twopoint718/pomodoro-timer/pomodorov2/pomodorov2.kicad_sch

## KiCad design pomodorov2/pomodorov2.kicad_sch (2022-04-18)

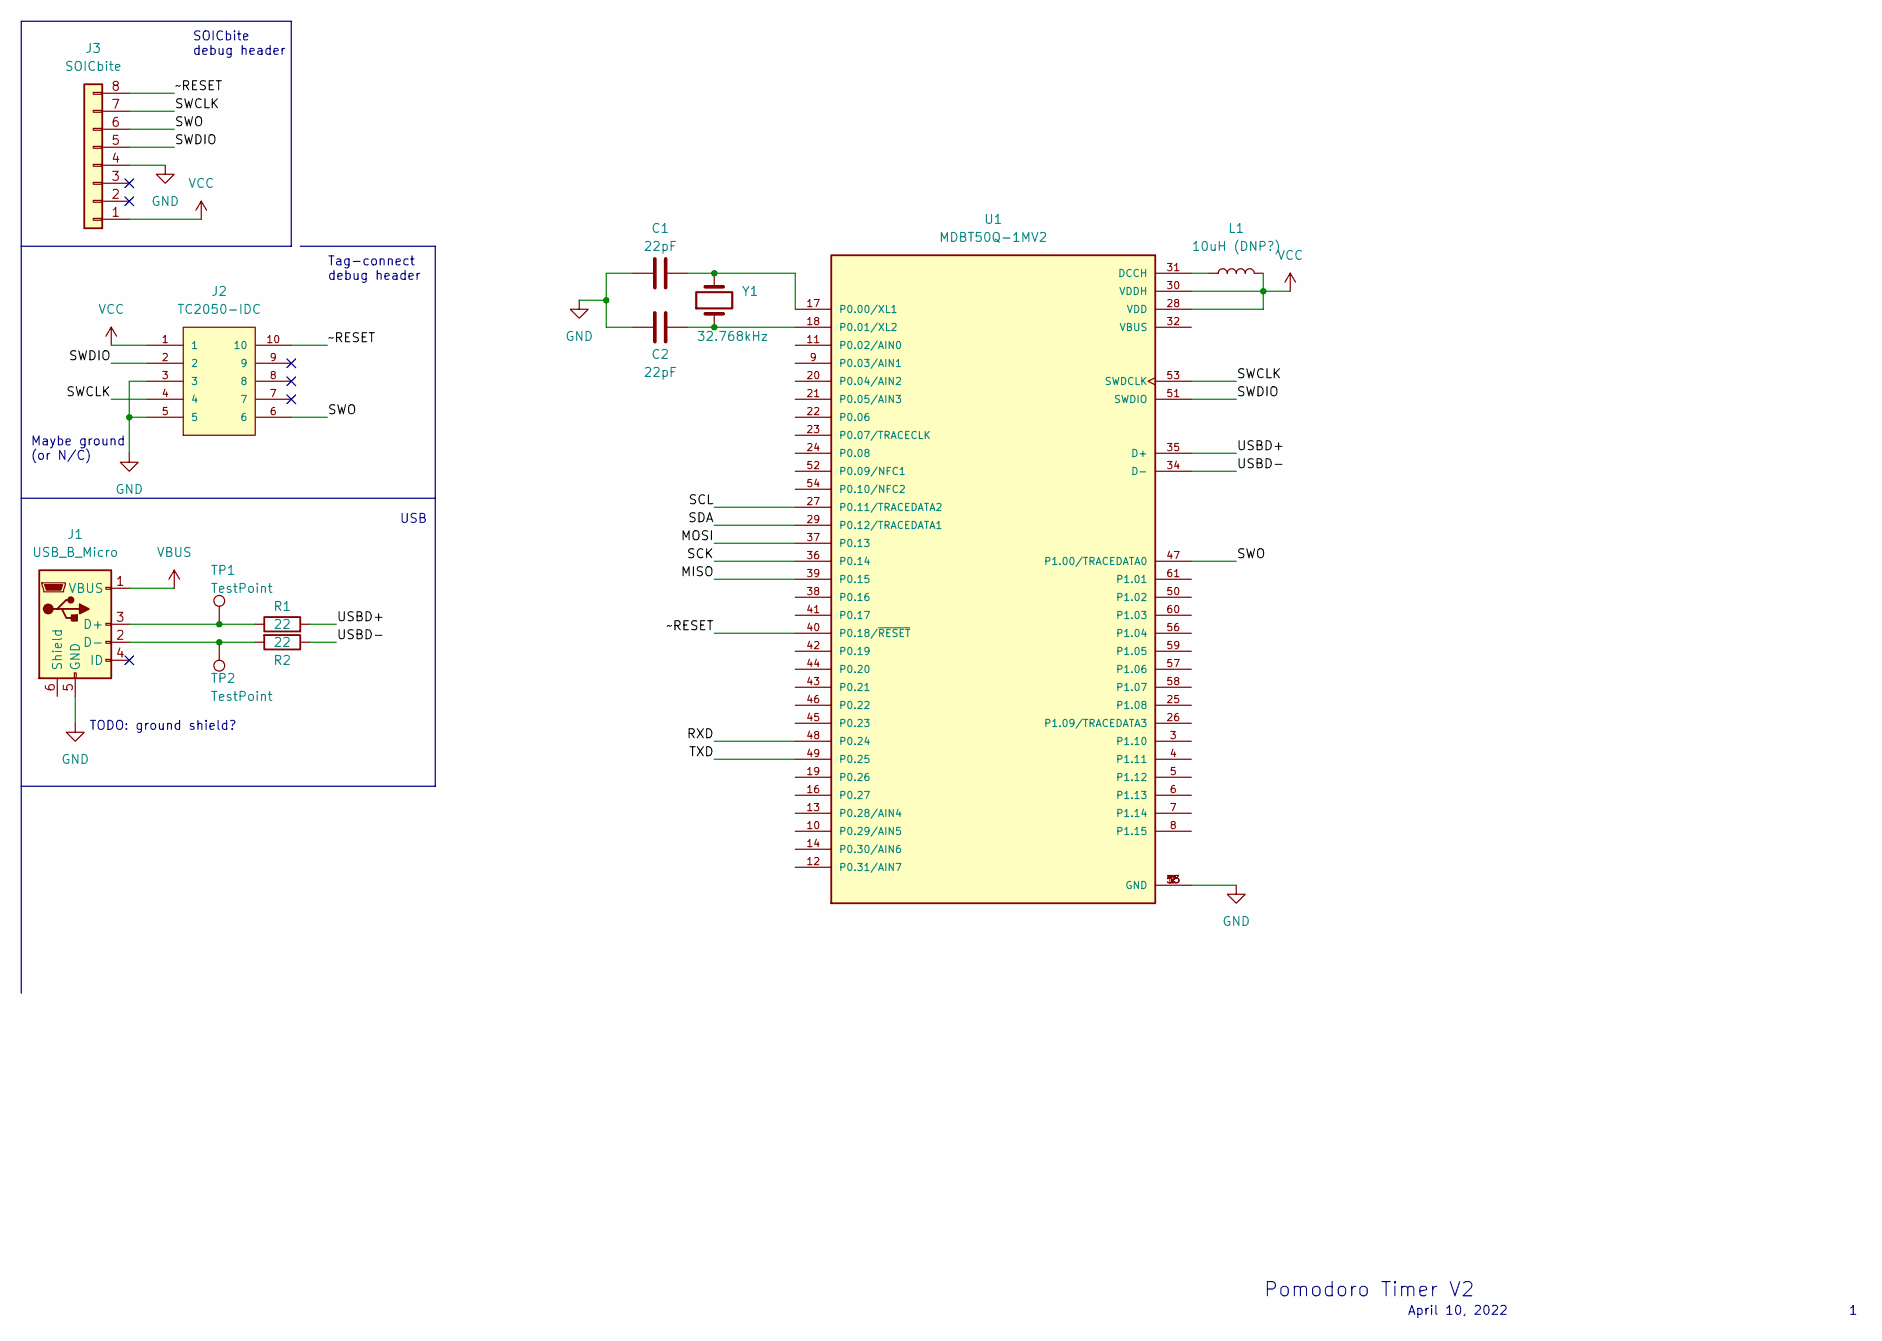
[picture p4: schematic pomodorov2.kicad_sch]

Parts:
C1, C2: 22pF; C_0805_2012Metric_Pad1.18x1.45mm_HandSolder
J1: USB_B_Micro; USB_Micro-B_Amphenol_10104110_Horizontal
J2: TC2050-IDC; TAG-CONNECT_TC2050-IDC; PARTREV A
J3: SOICbite; SOIC_clipProgSmall
L1: 10uH (DNP?); L_0805_2012Metric_Pad1.05x1.20mm_HandSolder
R1, R2: 22; R_0805_2012Metric_Pad1.20x1.40mm_HandSolder
TP1, TP2: TestPoint; TestPoint_Pad_D1.0mm
U1: MDBT50Q-1MV2; XCVR_MDBT50Q-1MV2; PARTREV H
Y1: 32.768kHz; Crystal_SMD_2012-2Pin_2.0x1.2mm_HandSoldering

Connections:
GND: C1.1, C2.1, J1.5 (GND), J2.3, J2.5, J3.4, U1.1 (GND), U1.2 (GND), U1.15 (GND), U1.33 (GND), U1.55 (GND)
MISO: U1.39 (P0.15)
MOSI: U1.37 (P0.13)
unnamed: C1.2, U1.17 (P0.00/XL1), Y1.2
unnamed: C2.2, U1.18 (P0.01/XL2), Y1.1
unnamed: J1.2 (D-), R2.2, TP2.1
unnamed: J1.3 (D+), R1.1, TP1.1
unnamed: L1.1, U1.31 (DCCH)
RXD: U1.48 (P0.24)
SCK: U1.36 (P0.14)
SCL: U1.27 (P0.11/TRACEDATA2)
SDA: U1.29 (P0.12/TRACEDATA1)
SWCLK: J2.4, J3.7, U1.53 (SWDCLK)
SWDIO: J2.2, J3.5, U1.51 (SWDIO)
SWO: J2.6, J3.6, U1.47 (P1.00/TRACEDATA0)
TXD: U1.49 (P0.25)
USBD+: R1.2, U1.35 (D+)
USBD-: R2.1, U1.34 (D-)
VBUS: J1.1 (VBUS)
VCC: J2.1, J3.1, L1.2, U1.28 (VDD), U1.30 (VDDH)
~RESET: J2.10, J3.8, U1.40 (P0.18/~RESET)

Notes on the sheet:
Maybe ground (or N/C)
USB
April 10, 2022
TODO: ground shield?
Pomodoro Timer V2
SOICbite debug header
Tag-connect debug header
